ide/pico-door-sensor/schematic/Pico W Garage Door Sensor.kicad_sch

## KiCad design schematic/Pico W Garage Door Sensor.kicad_sch (2022-10-12)

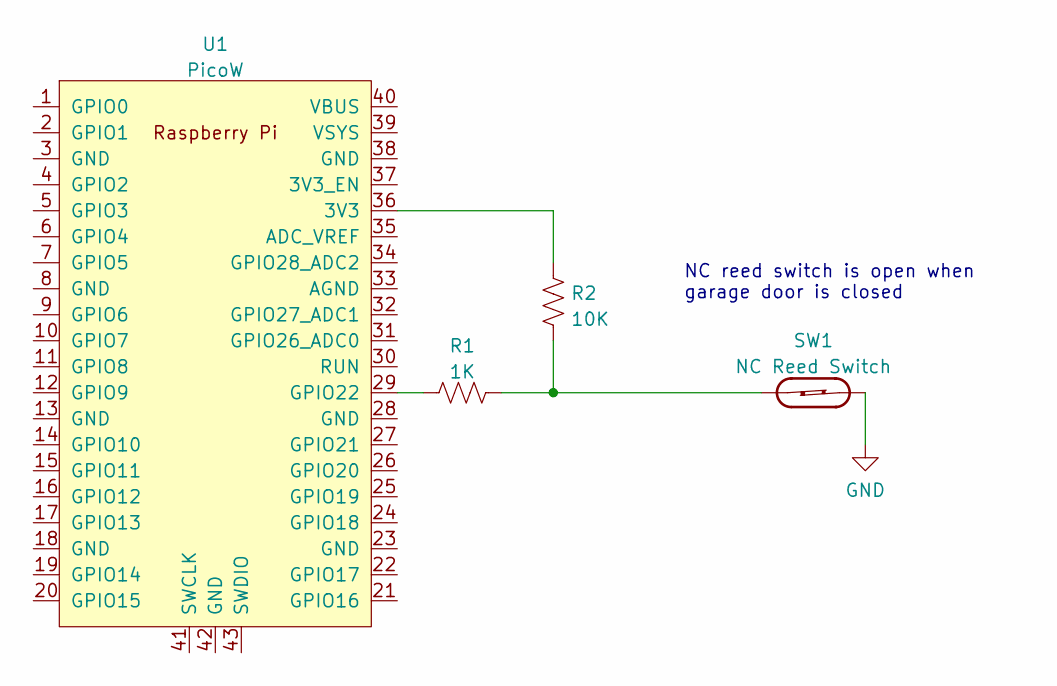
[picture p2: schematic Pico W Garage Door Sensor.kicad_sch]

Parts:
R1: 1K
R2: 10K
SW1: NC Reed Switch
U1: PicoW; RPi_Pico_SMD_TH

Connections:
unnamed: R1.1, U1.29 (GPIO22)
unnamed: R1.2, R2.2, SW1.1
unnamed: R2.1, U1.36 (3V3)

Notes on the sheet:
NC reed switch is open when garage door is closed
